MonisRaza123/mood_lamp/images/back.jpg

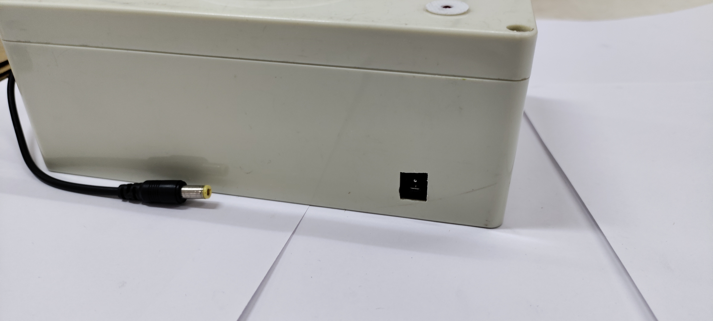
images/back.jpg
