MonisRaza123/mood_lamp/images/green1.jpeg

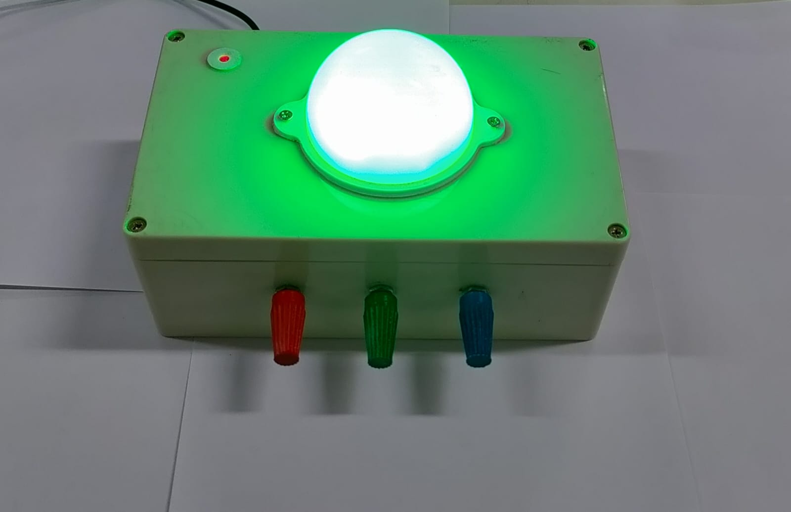
images/green1.jpeg
