MonisRaza123/mood_lamp/images/red1.jpeg

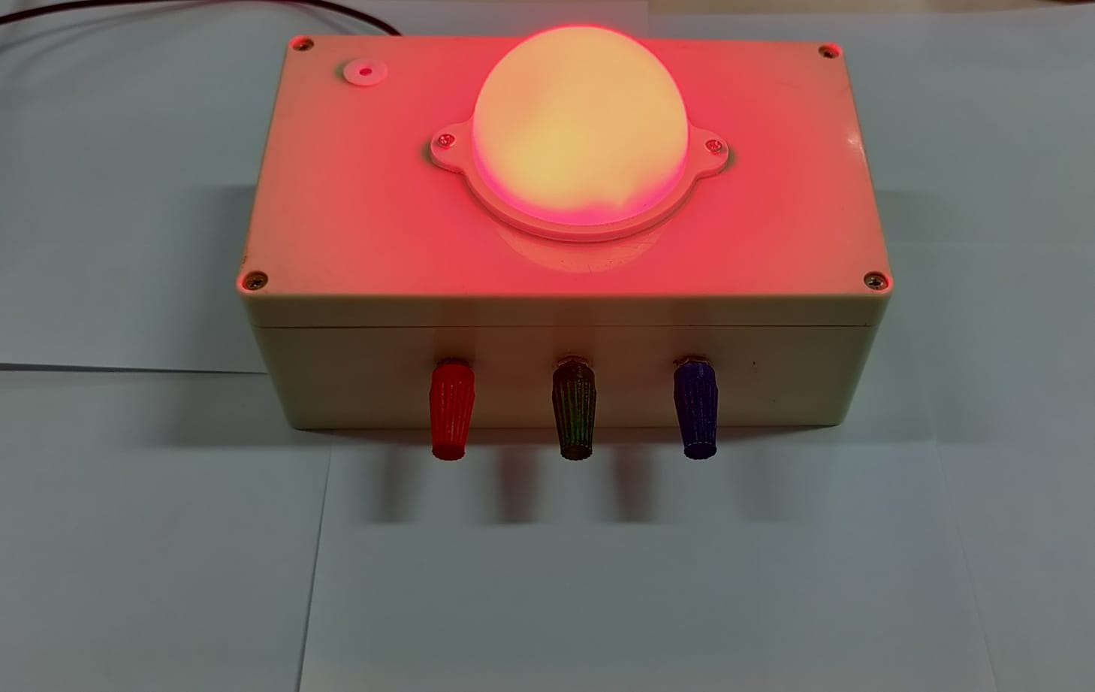
images/red1.jpeg
