MonisRaza123/mood_lamp/images/rgb_led.png

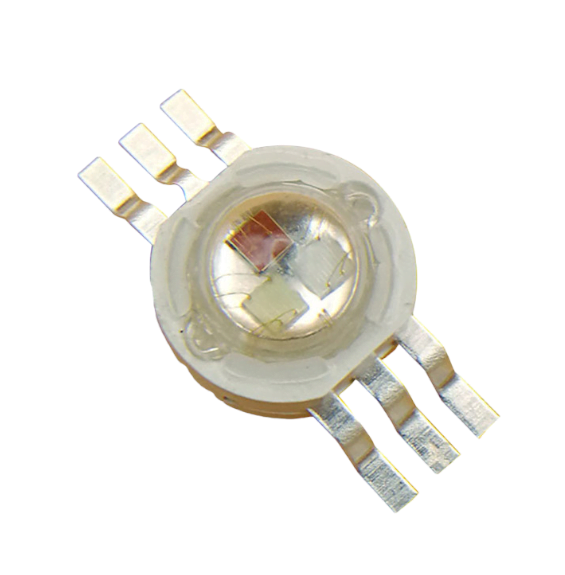
images/rgb_led.png
